CreatorKanata/terra-guard-ai-digikey-make-one-2026/src/FRDM-MCXN947/terra-guard-ai/app/npu_infer.c

/*
 * TerraGuard AI — FRDM-MCXN947
 * npu_infer: eIQ Neutron NPU カラス検出推論（2クラス: not_crow / crow）の実装
 *
 * 入力テンソル整形は tools/ml/build_trainset.py と厳密に一致させる:
 *   ch0 thermal_abs : サーマル(℃) を [T_VMIN,T_VMAX] で 0..1
 *   ch1 thermal_fg  : サーマル前景(℃,>=0) を [0,T_FG_MAX] で 0..1
 *   ch2 distance    : 距離(mm) を [0,D_VMAX] で 0..1（無効/負値は遠方=D_VMAX相当）
 *   ch3 distance_fg : 距離前景(mm,>=0) を [0,D_FG_MAX] で 0..1
 * モデル入力は 24×24×4。形状合わせ:
 *   サーマル: ファームで「90度右回転＋中央24行crop」済みの 24×24 をそのまま使う（無加工）。
 *   距離    : 8×8 を最近傍3倍 upsample して 24×24。
 * 向き: ファームがサーマルを回転＋crop済みで送るため、ここでは反転等を行わない。距離も反転なし。
 *
 * Copyright 2026 TerraGuard
 * SPDX-License-Identifier: BSD-3-Clause
 */
#include "npu_infer.h"
#include "model.h"
#include "thermal_mlx90640.h" /* THERMAL_OUT_W/H (24×24) */
#include "fsl_debug_console.h"

/* 正規化レンジ（build_trainset.py と一致させること）。 */
#define T_VMIN   15.0f
#define T_VMAX   45.0f
#define T_FG_MAX 5.0f
#define D_VMAX   4000.0f
#define D_FG_MAX 500.0f

/* サーマルはファーム側で「90度右回転＋中央24行crop」済みの 24×24 で渡される
   （thermal_mlx90640.h: THERMAL_OUT_W/H=24）。モデル入力も 24×24 なので無加工。 */
#define TW_ THERMAL_OUT_W  /* = 24（サーマル入力の幅）*/
#define TH_ THERMAL_OUT_H  /* = 24（サーマル入力の高さ）*/
#define DG 8    /* distance grid */

/* モデル入力（24×24×4）。サーマル24×24と距離8×8(→3倍で24×24)を4chに重ねる。 */
#define IN_H 24
#define IN_W 24
#define IN_C 4
#define IN_SIZE (IN_H * IN_W * IN_C)

/* 入力量子化（学習時の int8 量子化に一致。scale=1/255, zero_point=-128）。
   float x(0..1) → int8 q = round(x*255) - 128 = round(x/scale) + zp。
   model.cpp は per-tensor int8 を前提とするため固定値で再現する。 */
#define IN_SCALE 0.003921568859f
#define IN_ZP    (-128)

static bool s_ready;

static inline float clamp01(float v)
{
    if (v < 0.0f) return 0.0f;
    if (v > 1.0f) return 1.0f;
    return v;
}

static inline int8_t quantize01(float x01)
{
    /* q = round(x/scale) + zp。x01 は 0..1 にクリップ済み前提。 */
    int q = (int)(x01 / IN_SCALE + 0.5f) + IN_ZP;
    if (q < -128) q = -128;
    if (q > 127)  q = 127;
    return (int8_t)q;
}

bool npu_infer_init(void)
{
    tensor_dims_t dims;
    tensor_type_t type;
    uint8_t *in = MODEL_GetInputTensorData(&dims, &type);

    s_ready = false;
    if (in == NULL)
    {
        PRINTF("npu_infer: 入力テンソル取得失敗\r\n");
        return false;
    }
    /* 期待: [1,24,24,4] int8。 */
    if (type != kTensorType_INT8 || dims.size != 4 ||
        dims.data[1] != IN_H || dims.data[2] != IN_W || dims.data[3] != IN_C)
    {
        PRINTF("npu_infer: 入力形状/型が想定外 (size=%d [%d,%d,%d,%d] type=%d)\r\n",
               (int)dims.size, (int)dims.data[0], (int)dims.data[1],
               (int)dims.data[2], (int)dims.data[3], (int)type);
        return false;
    }
    s_ready = true;
    return true;
}

bool npu_infer_run(const float *thermalRot, const float *thermalFgRot,
                   const int16_t *dist8x8, const int16_t *distFg8x8,
                   npu_result_t *out)
{
    if (!s_ready || out == NULL)
    {
        return false;
    }

    tensor_dims_t dims;
    tensor_type_t type;
    int8_t *in = (int8_t *)MODEL_GetInputTensorData(&dims, &type);
    if (in == NULL)
    {
        return false;
    }

    /* 入力テンソルは [H=24][W=24][C=4] の行優先。in[(y*IN_W + x)*IN_C + c]。
       サーマルはファーム側で「90度右回転＋中央24行crop」済みの 24×24（行優先）で
       モデル入力と同寸法なので無加工。距離8×8は最近傍3倍で24×24に展開。
       build_trainset.py の前処理（サーマル無加工 / 距離3倍upsample）と厳密一致。 */
    for (int y = 0; y < IN_H; y++)
    {
        for (int x = 0; x < IN_W; x++)
        {
            float ch0, ch1, ch2, ch3;

            /* --- ch0/ch1: サーマル（24×24 をそのまま, 行優先） --- */
            int tidx = y * TW_ + x;    /* TW_=24 */
            float tc = thermalRot[tidx];
            float tf = thermalFgRot[tidx];
            ch0 = clamp01((tc - T_VMIN) / (T_VMAX - T_VMIN));
            ch1 = clamp01((tf - 0.0f) / (T_FG_MAX - 0.0f));

            /* --- ch2/ch3: 距離（8×8→最近傍3倍, 反転なし） --- */
            int dr = y / (IN_H / DG);   /* y/3 → 0..7 */
            int dc = x / (IN_W / DG);   /* x/3 → 0..7 */
            int didx = dr * DG + dc;
            float dmm = (float)dist8x8[didx];
            if (dmm < 0.0f) dmm = D_VMAX;     /* 無効ゾーンは遠方相当（build_trainset と一致） */
            float dfg = (float)distFg8x8[didx];
            if (dfg < 0.0f) dfg = 0.0f;
            ch2 = clamp01((dmm - 0.0f) / (D_VMAX - 0.0f));
            ch3 = clamp01((dfg - 0.0f) / (D_FG_MAX - 0.0f));

            int base = (y * IN_W + x) * IN_C;
            in[base + 0] = quantize01(ch0);
            in[base + 1] = quantize01(ch1);
            in[base + 2] = quantize01(ch2);
            in[base + 3] = quantize01(ch3);
        }
    }

    if (MODEL_RunInference() != kStatus_Success)
    {
        return false;
    }

    /* 出力 [1,2] int8。逆量子化して softmax 確率に戻す（per-tensor int8）。
       出力スケールは学習時 scale=1/256, zp=-128（make時のログ参照）。 */
    int8_t *outq = (int8_t *)MODEL_GetOutputTensorData(&dims, &type);
    if (outq == NULL || dims.data[dims.size - 1] < 2)
    {
        return false;
    }
    const float outScale = 0.00390625f; /* 1/256 */
    const int   outZp    = -128;
    float p0 = ((int)outq[0] - outZp) * outScale; /* not_crow */
    float p1 = ((int)outq[1] - outZp) * outScale; /* crow */

    out->p_crow     = p1;
    out->crow       = (p1 >= p0);
    out->confidence = out->crow ? p1 : p0;
    return true;
}
